RoboticsBrno/RB0005-UniversalStepDown/evaluation/assets/setup1.jpg

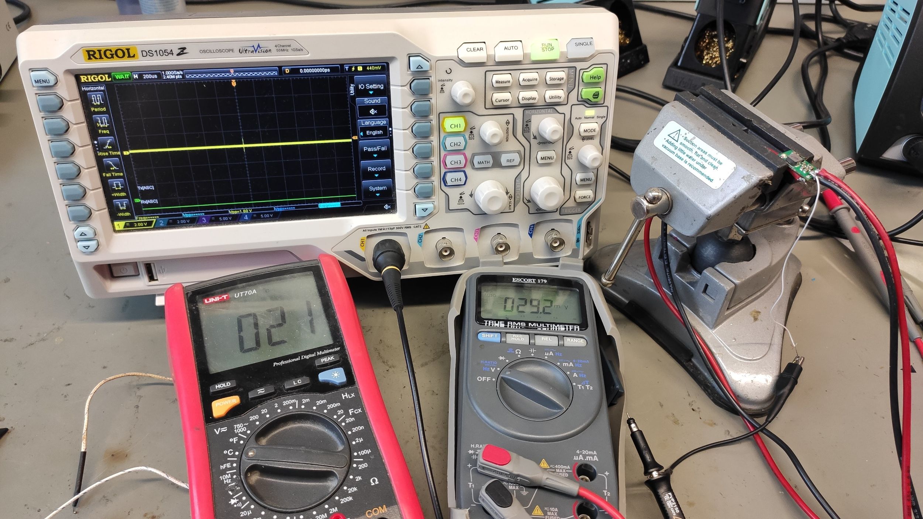
evaluation/assets/setup1.jpg
