RoboticsBrno/RB0005-UniversalStepDown/evaluation/assets/photo.jpg

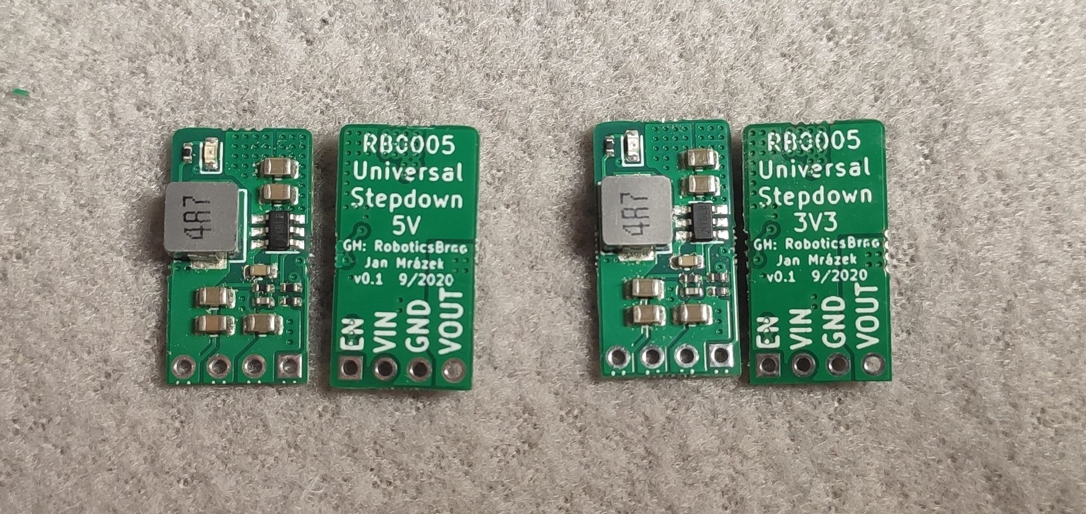
evaluation/assets/photo.jpg
