RoboticsBrno/RB0005-UniversalStepDown/evaluation/assets/waveforms/v0.1-3V3-3.png

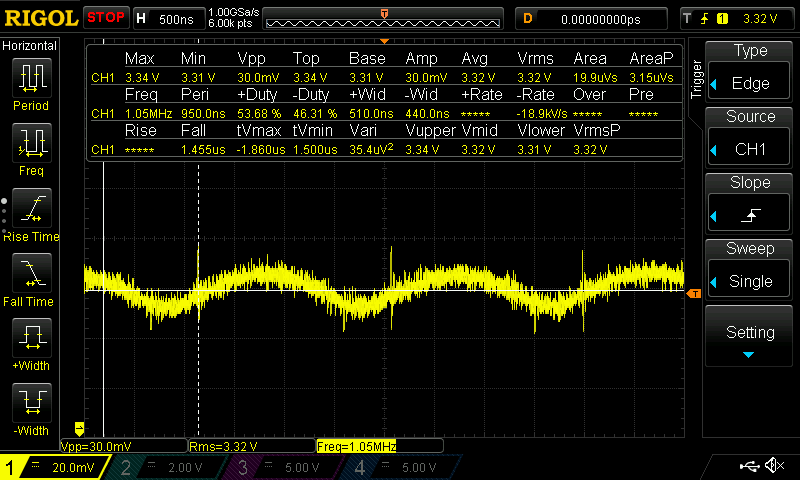
evaluation/assets/waveforms/v0.1-3V3-3.png
