RoboticsBrno/RB0005-UniversalStepDown/evaluation/assets/waveforms/v0.1-3V3-11.png

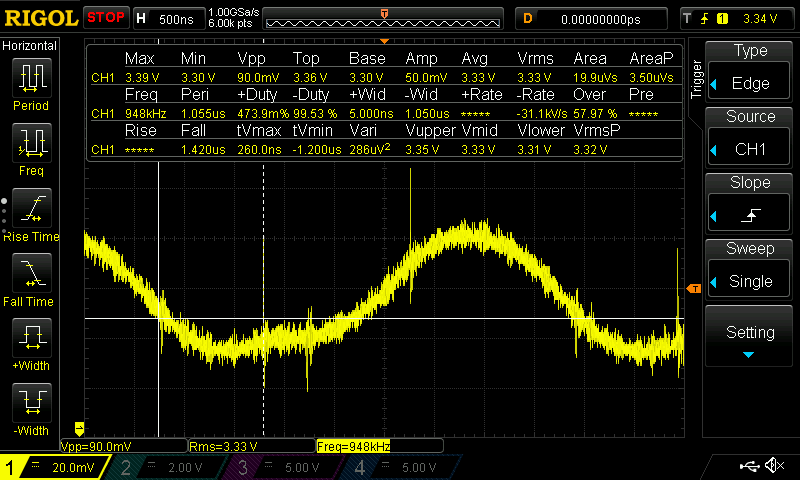
evaluation/assets/waveforms/v0.1-3V3-11.png
