RoboticsBrno/RB0005-UniversalStepDown/evaluation/assets/waveforms/v0.2-5V-12.png

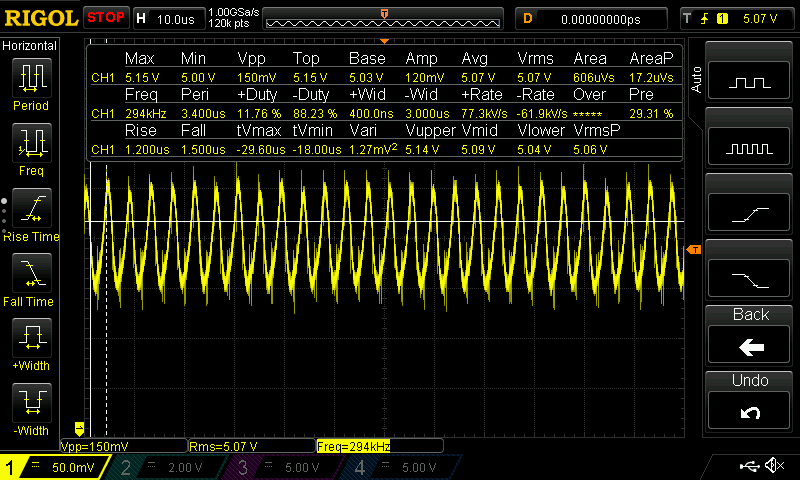
evaluation/assets/waveforms/v0.2-5V-12.png
